ArsenioDev/AERONET-Heated-wet-sensor/IMG/image000000.JPG

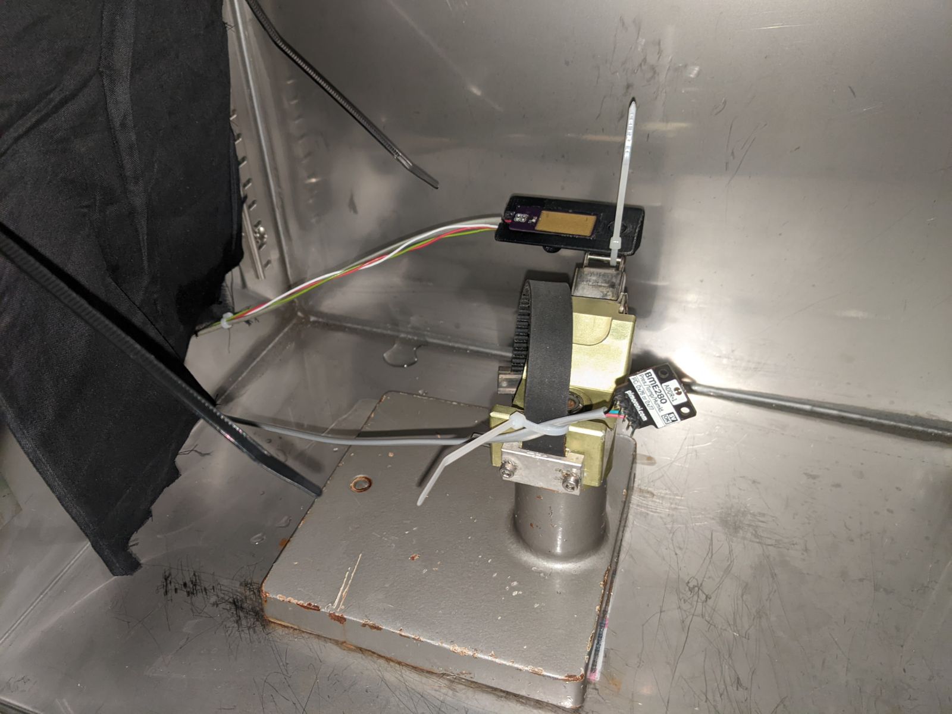
IMG/image000000.JPG
