ArsenioDev/AERONET-Heated-wet-sensor/IMG/IMG-4534.jpg

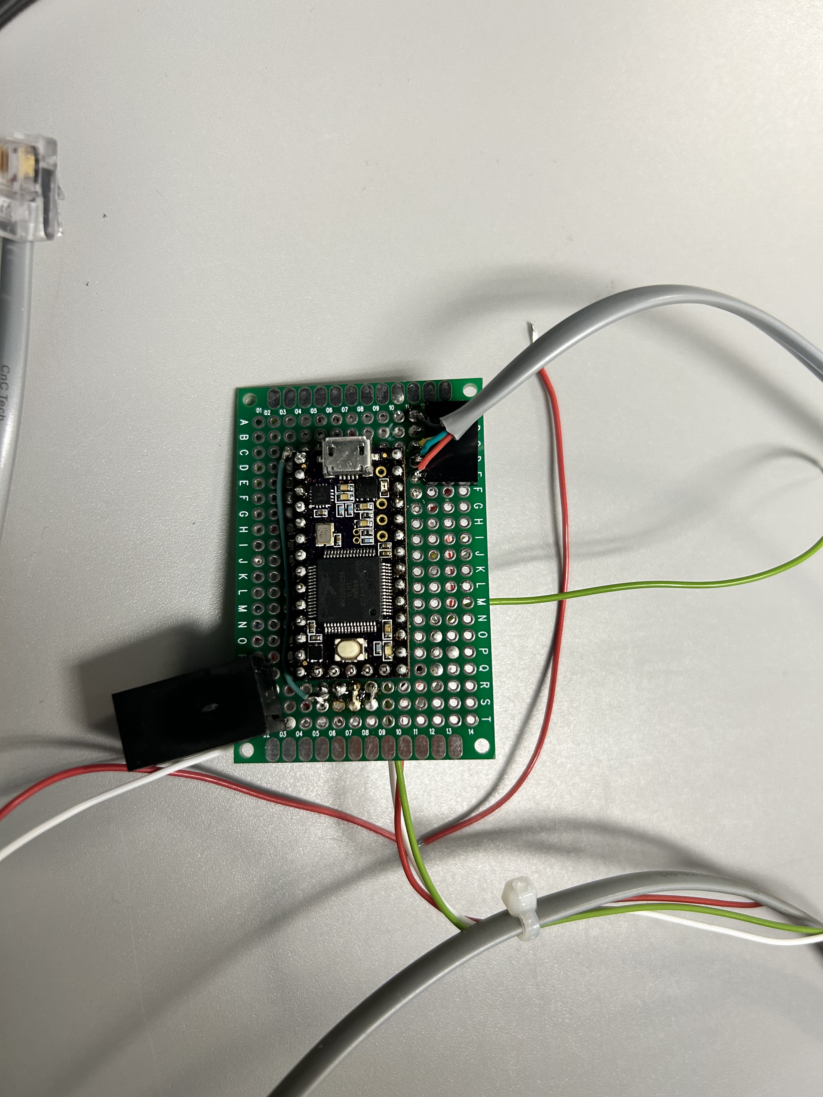
IMG/IMG-4534.jpg
