ArsenioDev/AERONET-Heated-wet-sensor/IMG/IMG-4535.jpg

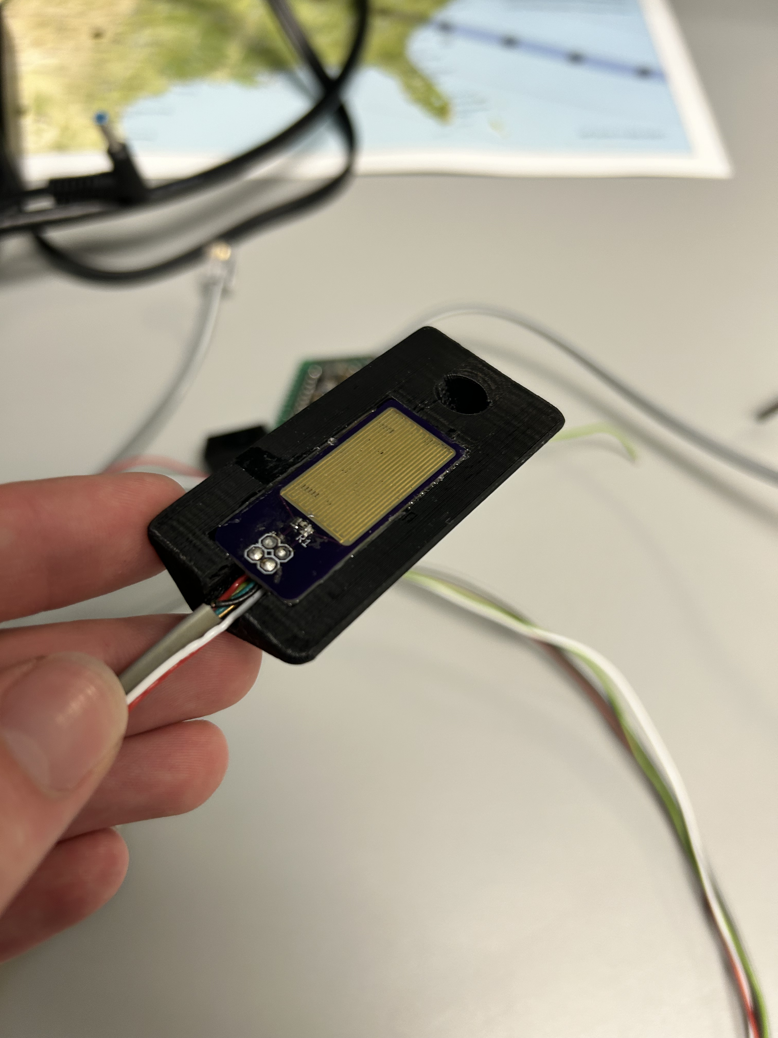
IMG/IMG-4535.jpg
