ArsenioDev/AERONET-Heated-wet-sensor/IMG/IMG-4536.jpg

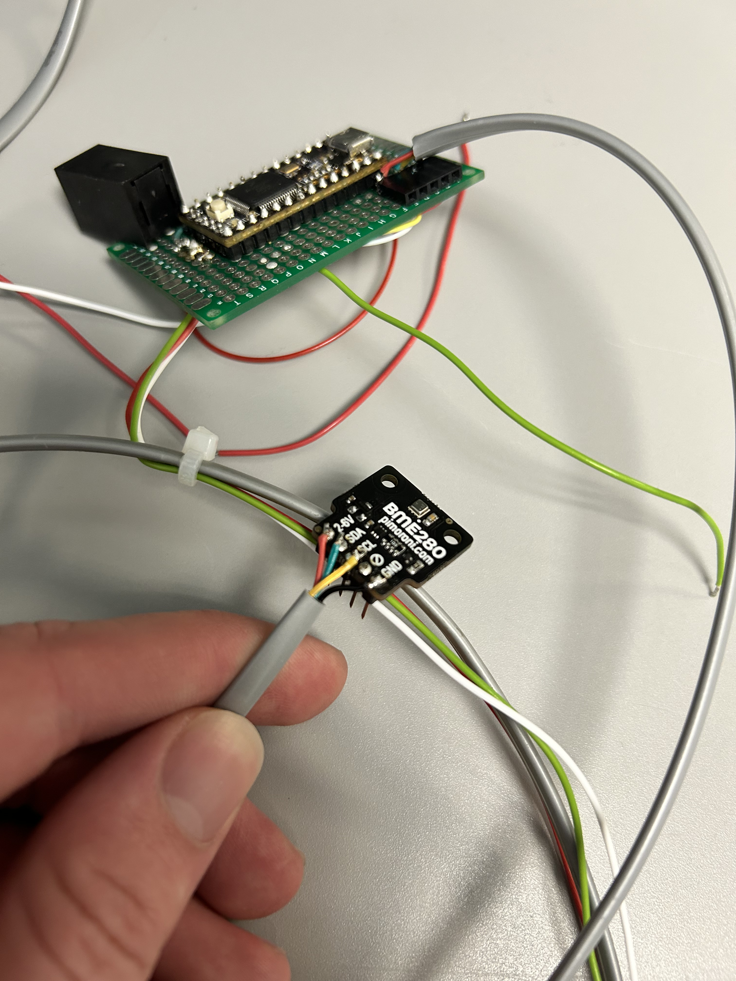
IMG/IMG-4536.jpg
