ArsenioDev/AERONET-Heated-wet-sensor/IMG/IMG-4537.jpg

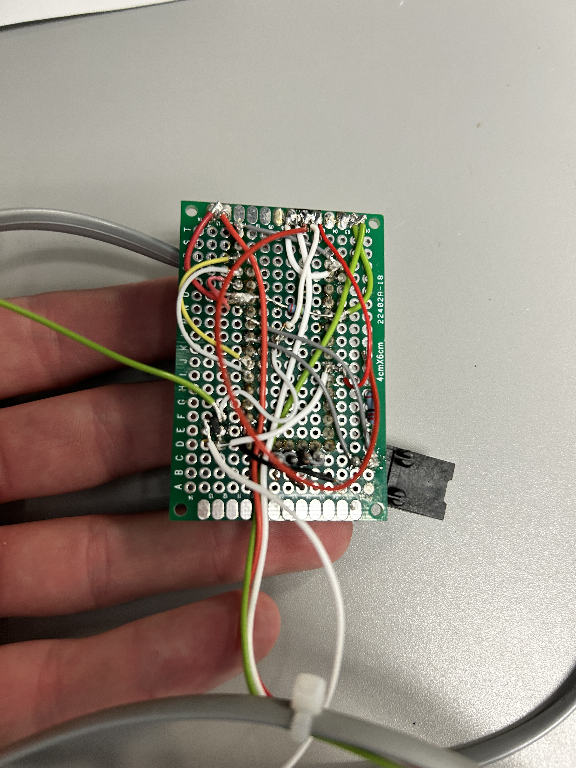
IMG/IMG-4537.jpg
