ArsenioDev/AERONET-Heated-wet-sensor/IMG/IMG-4541.jpg

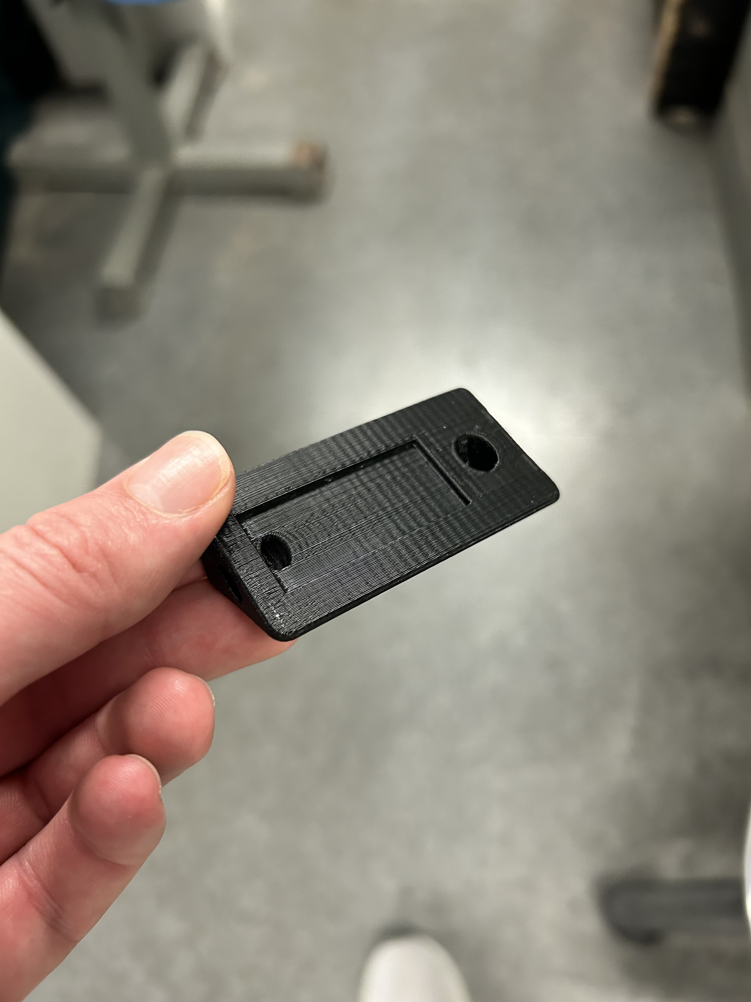
IMG/IMG-4541.jpg
