ArsenioDev/AERONET-Heated-wet-sensor/IMG/IMG-4542.jpg

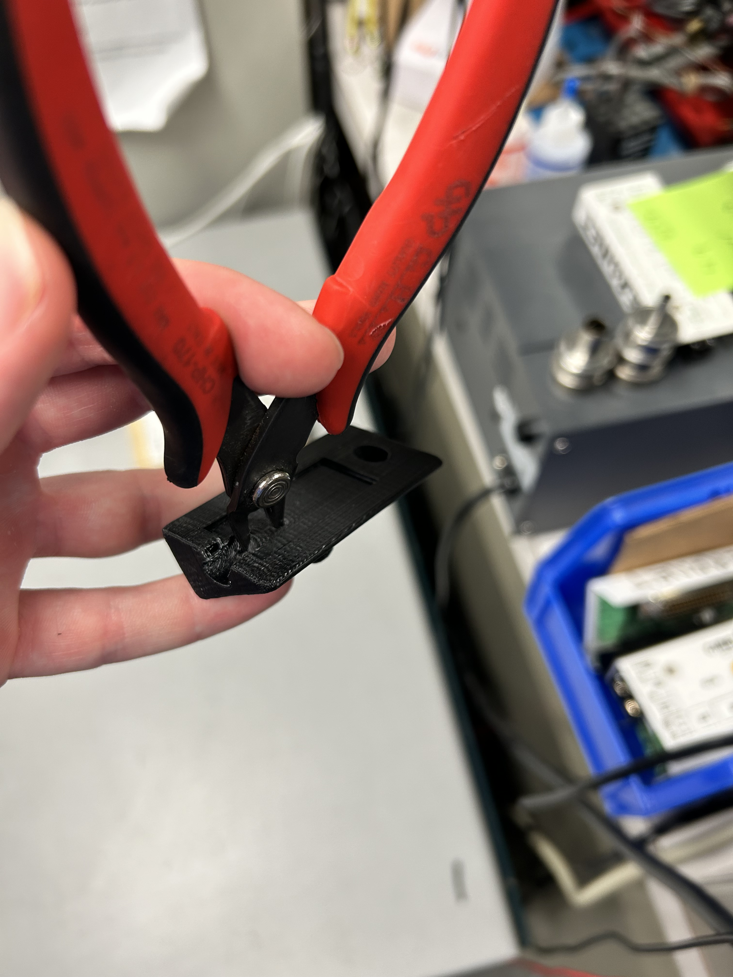
IMG/IMG-4542.jpg
