ArsenioDev/AERONET-Heated-wet-sensor/IMG/IMG-4543.jpg

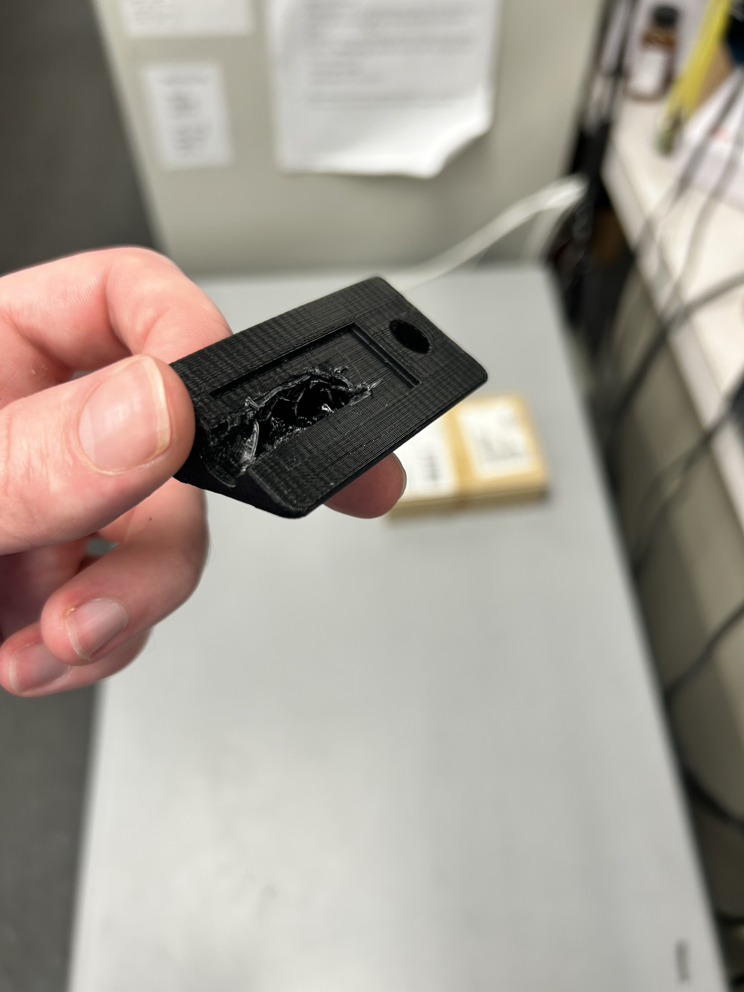
IMG/IMG-4543.jpg
