ArsenioDev/AERONET-Heated-wet-sensor/IMG/IMG-4544.jpg

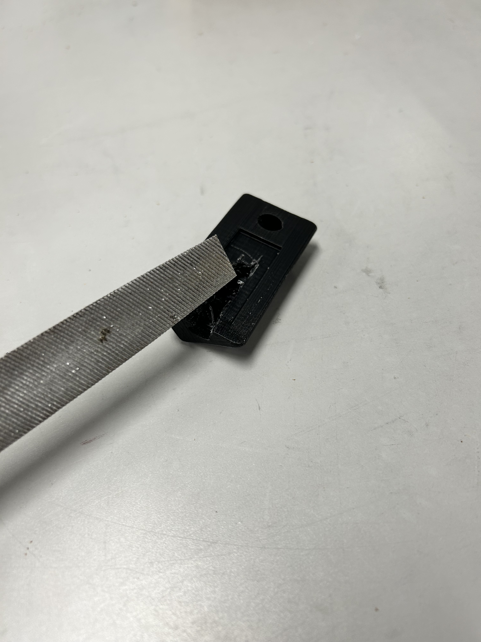
IMG/IMG-4544.jpg
