ArsenioDev/AERONET-Heated-wet-sensor/IMG/IMG-4545.jpg

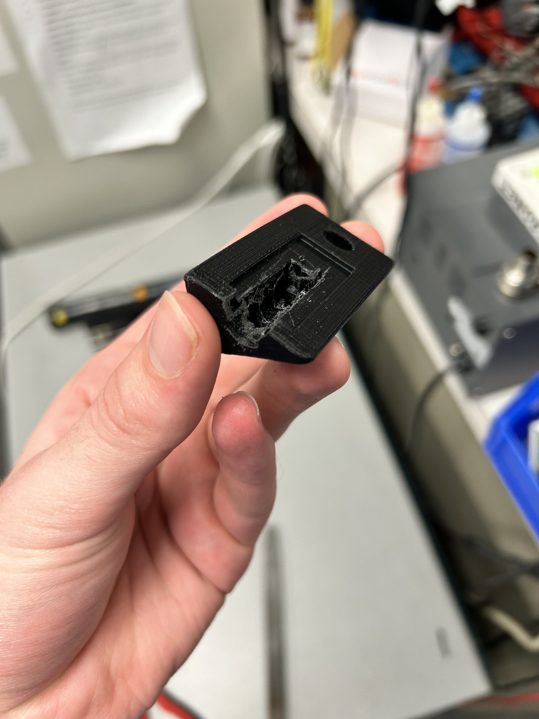
IMG/IMG-4545.jpg
