ArsenioDev/AERONET-Heated-wet-sensor/IMG/IMG-4546.jpg

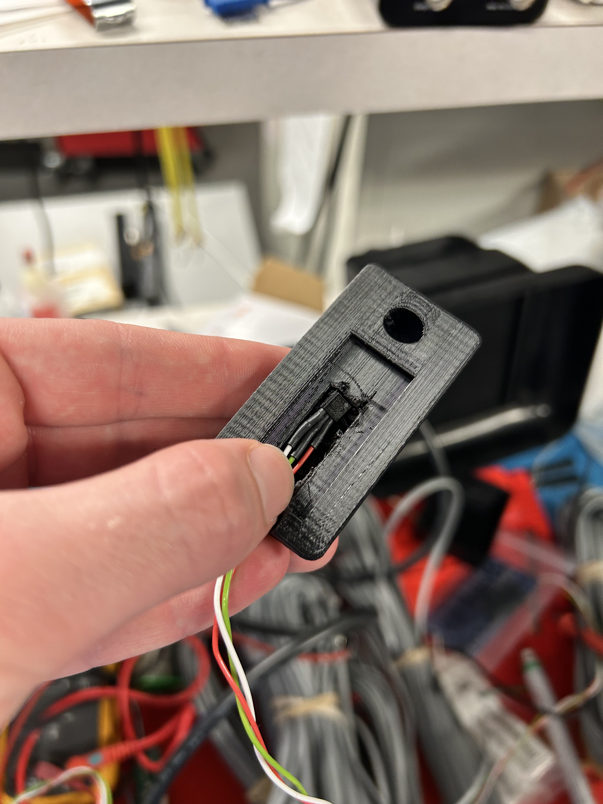
IMG/IMG-4546.jpg
